Thomascountz/aux/Hexo/bitmap.png

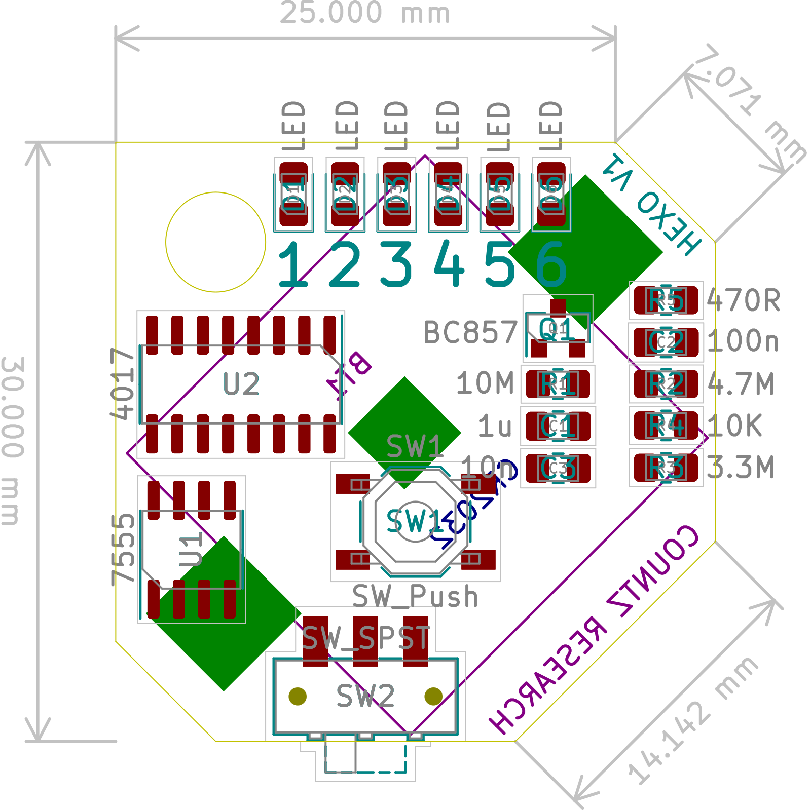
Hexo/bitmap.png
