Thomascountz/aux/Hexo/Hexo-brd.png

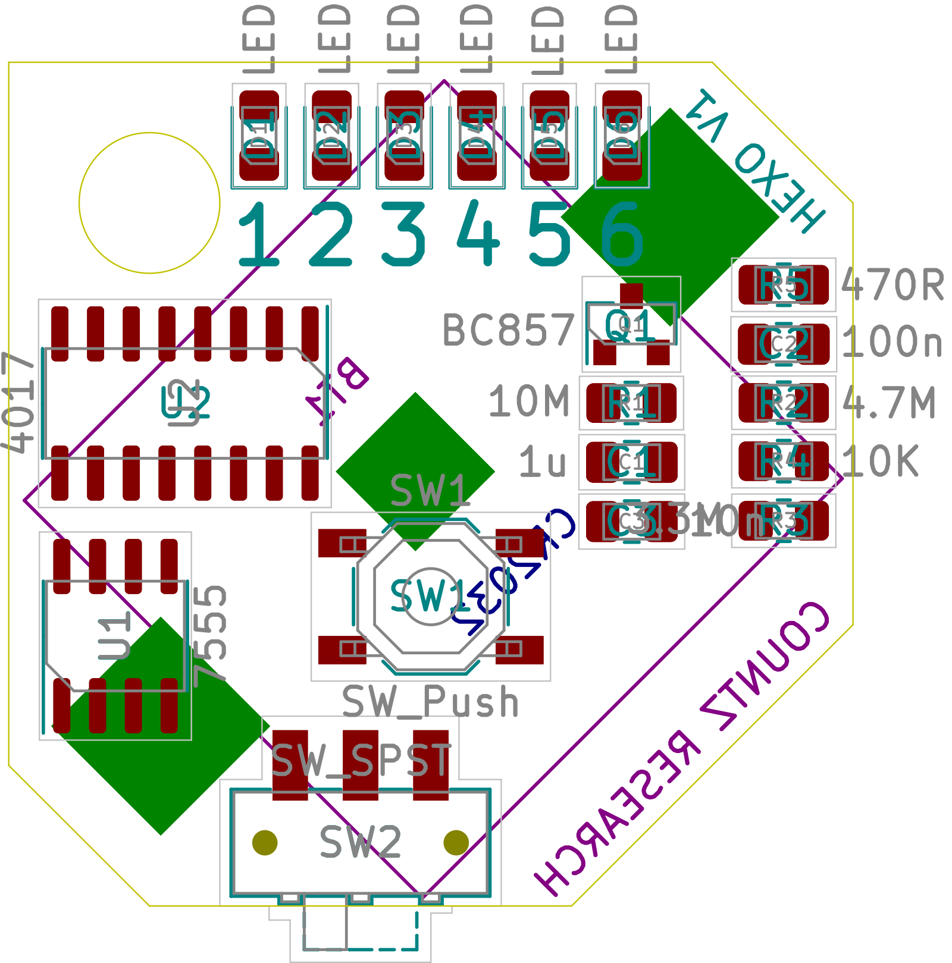
Hexo/Hexo-brd.png
