Thomascountz/aux/Hexo/hexo_final_back.png

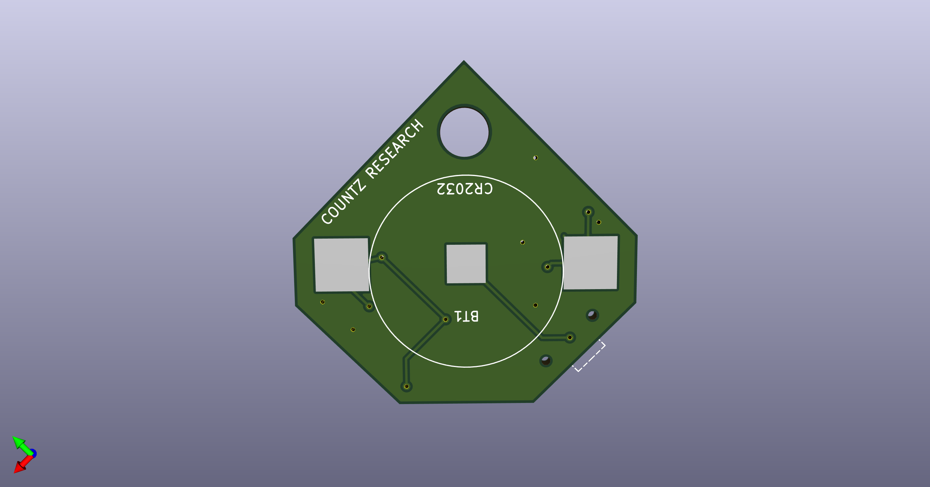
Hexo/hexo_final_back.png
