Thomascountz/aux/Hexo/init_2_board_1.png

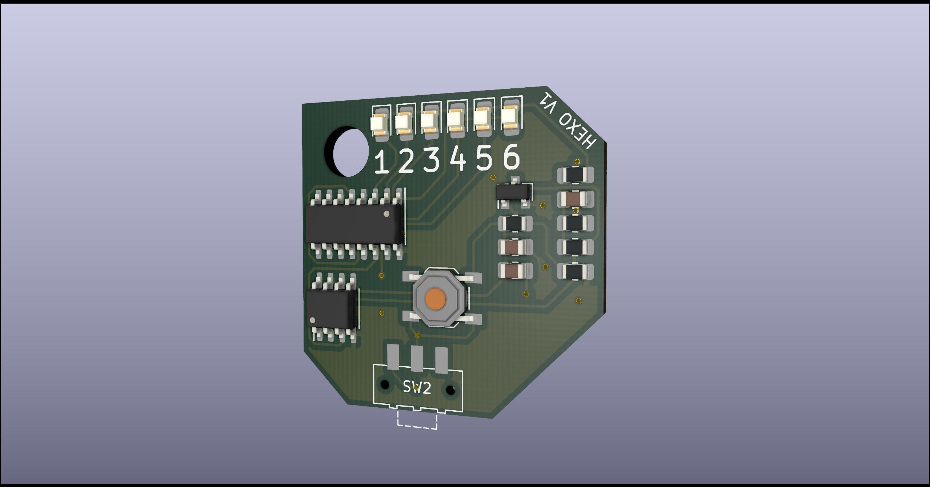
Hexo/init_2_board_1.png
