Thomascountz/aux/Hexo/init_board_3.png

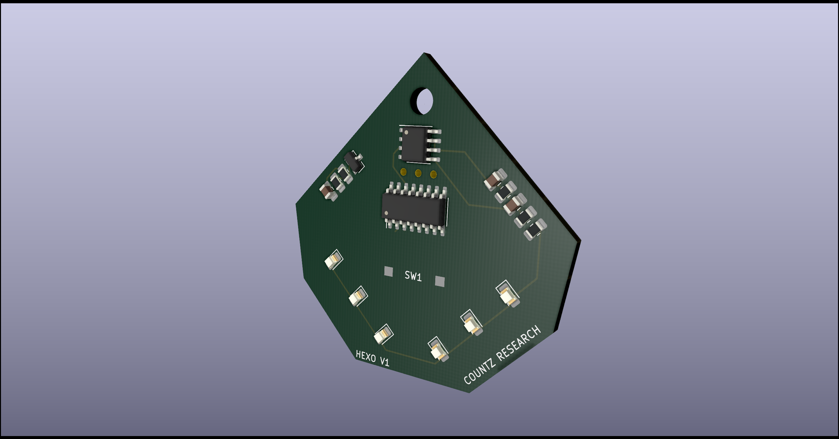
Hexo/init_board_3.png
