Thomascountz/aux/Hexo/init_board_4.png

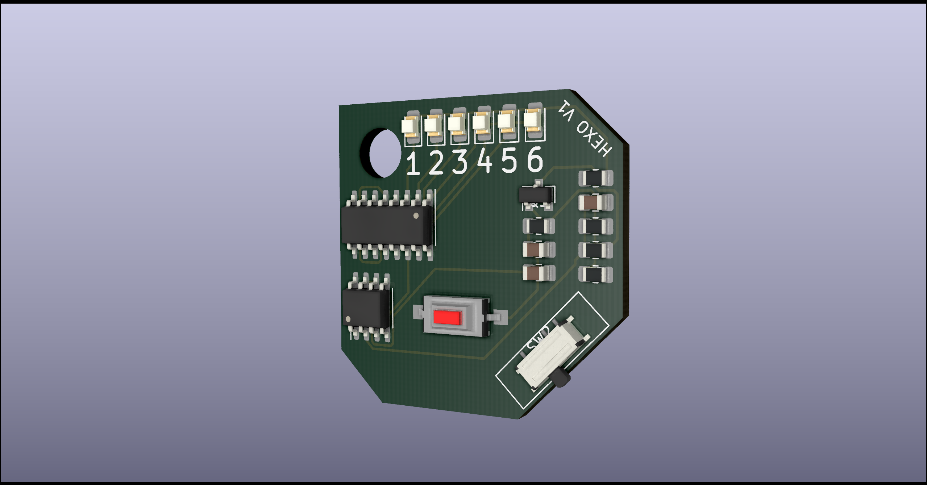
Hexo/init_board_4.png
