Thomascountz/aux/getting_to_blinky/ltspice_sim.asc

C1: cap; 1µ
D1: LED; QTLP690C
R1: res; 1K
R2: res; 470K
R3: res; 1K
U1: NE555
V1: voltage; 5
Named nets: 0, VCC
.tran 0 10 0
